Catmacey/DrumMachine/Source/json.h

/* 
 * File:   json.h
 * Author: Matt
 *
 * Created on 28 December 2014, 00:03
 */

#ifndef JSON_H
#define	JSON_H

#ifdef	__cplusplus
extern "C" {
#endif

/** P R O T O T Y P E S ******************************************************/
int8_t parseJSON( const char *value );  // Temporarily public for testing

#ifdef	__cplusplus
}
#endif

#endif	/* JSON_H */
